ZaubererHaft/IR-Cam-DIY/Inc/user_interface.h

#ifndef CAM_USER_INTERFACE_H
#define CAM_USER_INTERFACE_H

#include <stdint.h>

#include "config.h"

uint32_t UserInterface_Init(void);

int32_t UserInterface_ShowingAnyMenuOrDialog(void);

void UserInterface_Draw(void);

void UserInterface_RedrawIRImageIfNecessary(float *image);

void UserInterface_PutAnalogData(const uint16_t data[3]);

void UserInterface_ConfigObserver(Config config);

void UserInterface_ShowError(const char *text);

#endif //CAM_USER_INTERFACE_H
