ZaubererHaft/IR-Cam-DIY/Inc/ui_constants.h

#ifndef CAM_UI_CONSTANTS_H
#define CAM_UI_CONSTANTS_H

#define offset_x  0
#define offset_y  24
#define pixel_size  8
#define ir_width  32
#define ir_height  24
#define lcd_width 320
#define lcd_height 240
#define menu_width 200
#define menu_height 80
#define menu_font_size 16

#endif //CAM_UI_CONSTANTS_H
